MarkShaio/Badge-Test-Code/Latest PCB version/With 3D model/eagleUp/eagleUp_nRF24L01-Chip-v12_top.png

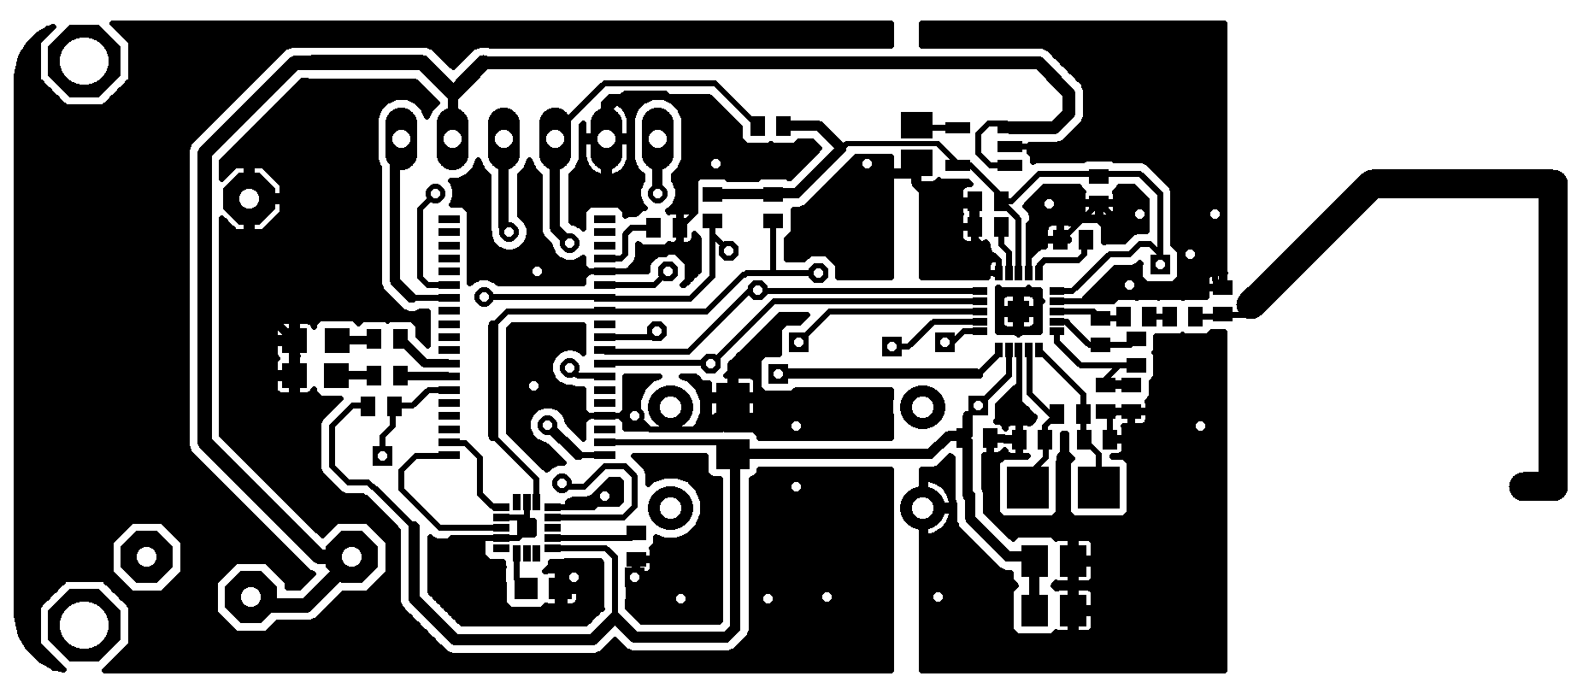
Latest PCB version/With 3D model/eagleUp/eagleUp_nRF24L01-Chip-v12_top.png
