MarkShaio/Badge-Test-Code/openbeacon-master_test/Netduino(AT91sam7)_BaseStation/openbeacon-ethernet/application/openbeacon.h

/*
    This file is part of the SocioPatterns firmware
    Copyright (C) 2008-2009 Istituto per l'Interscambio Scientifico I.S.I.
    You can contact us by email (isi@isi.it) or write to:
    ISI Foundation, Viale S. Severo 65, 10133 Torino, Italy. 

    This program was written by Ciro Cattuto <ciro.cattuto@gmail.com>

    This program is based on:
    OpenBeacon.org - OnAir protocol specification and definition
    Copyright 2006 Milosch Meriac <meriac@openbeacon.de>

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
    You should have received a copy of the GNU General Public License along
    with this program; if not, write to the Free Software Foundation, Inc.,
    51 Franklin Street, Fifth Floor, Boston, MA 02110-1301 USA.

    This file was modified on: April 1st, 2009
*/

#ifndef __OPENBEACON_H__
#define __OPENBEACON_H__

#define CONFIG_TRACKER_CHANNEL 81
#define CONFIG_PROX_CHANNEL 76

#define BEACONLOG_SIGHTING 0x01

#define XXTEA_BLOCK_COUNT 4

#define RFBPROTO_READER_ANNOUNCE 22
#define RFBPROTO_READER_COMMAND  23
#define RFBPROTO_BEACONTRACKER   24
#define RFBPROTO_PROXTRACKER     42
#define RFBPROTO_PROXREPORT      69

#define PROX_MAX 4

#define RFBFLAGS_ACK			0x01
#define RFBFLAGS_SENSOR			0x02
#define RFBFLAGS_INFECTED		0x04

/* RFBPROTO_READER_COMMAND related opcodes */
#define READER_CMD_NOP			0x00
#define READER_CMD_RESET		0x01
#define READER_CMD_RESET_CONFIG		0x02
#define READER_CMD_RESET_FACTORY	0x03
#define READER_CMD_RESET_WIFI		0x04
#define READER_CMD_SET_OID		0x05
/* RFBPROTO_READER_COMMAND related results */
#define READ_RES__OK			0x00
#define READ_RES__DENIED		0x01
#define READ_RES__UNKNOWN_CMD		0xFF

#define PACKED  __attribute__((__packed__))


typedef struct
{
  u_int8_t strength;
  u_int16_t oid_last_seen;
  u_int16_t powerup_count;
  u_int8_t reserved;
  u_int32_t seq;
} PACKED TBeaconTracker;

typedef struct
{
  u_int16_t oid_prox[PROX_MAX];
  u_int16_t seq;
} PACKED TBeaconProx;

typedef struct
{
  u_int8_t opcode, res;
  u_int32_t data[2];
} PACKED TBeaconReaderCommand;

typedef struct
{
  u_int8_t opcode, strength;
  u_int32_t uptime, ip;
} PACKED TBeaconReaderAnnounce;

typedef union
{
  TBeaconProx prox;
  TBeaconTracker tracker;
  TBeaconReaderCommand reader_command;
  TBeaconReaderAnnounce reader_announce;
} PACKED TBeaconPayload;

typedef struct
{
  u_int8_t proto;
  u_int16_t oid;
  u_int8_t flags;

  TBeaconPayload p;

  u_int16_t crc;
} PACKED TBeaconWrapper;

typedef union
{
  TBeaconWrapper pkt;
  u_int32_t block[XXTEA_BLOCK_COUNT];
  u_int8_t byte[XXTEA_BLOCK_COUNT * 4];
} PACKED TBeaconEnvelope;

typedef struct
{
  u_int16_t icrc16;
  u_int8_t protocol;
  u_int8_t interface;
  u_int16_t reader_id;
  u_int16_t size;
} PACKED TBeaconNetworkHdr;

/* BEACONLOG_SIGHTING */
typedef struct
{
  TBeaconNetworkHdr hdr;
  u_int32_t sequence;
  u_int32_t timestamp;
  TBeaconEnvelope log;
} PACKED TBeaconLogSighting;

typedef struct
{
  u_int8_t size;
  u_int8_t protocol;
  u_int8_t flags;
  u_int8_t strength;
  u_int32_t seq;
  u_int32_t oid;
  u_int16_t reserved;
  u_int16_t crc;
} PACKED localiserpacket;


#endif/*__OPENBEACON_H__*/
